beleata/fpga-led-panel-sram/hardware/pico-panel/preview/before-compact-connectors/placement-review.png

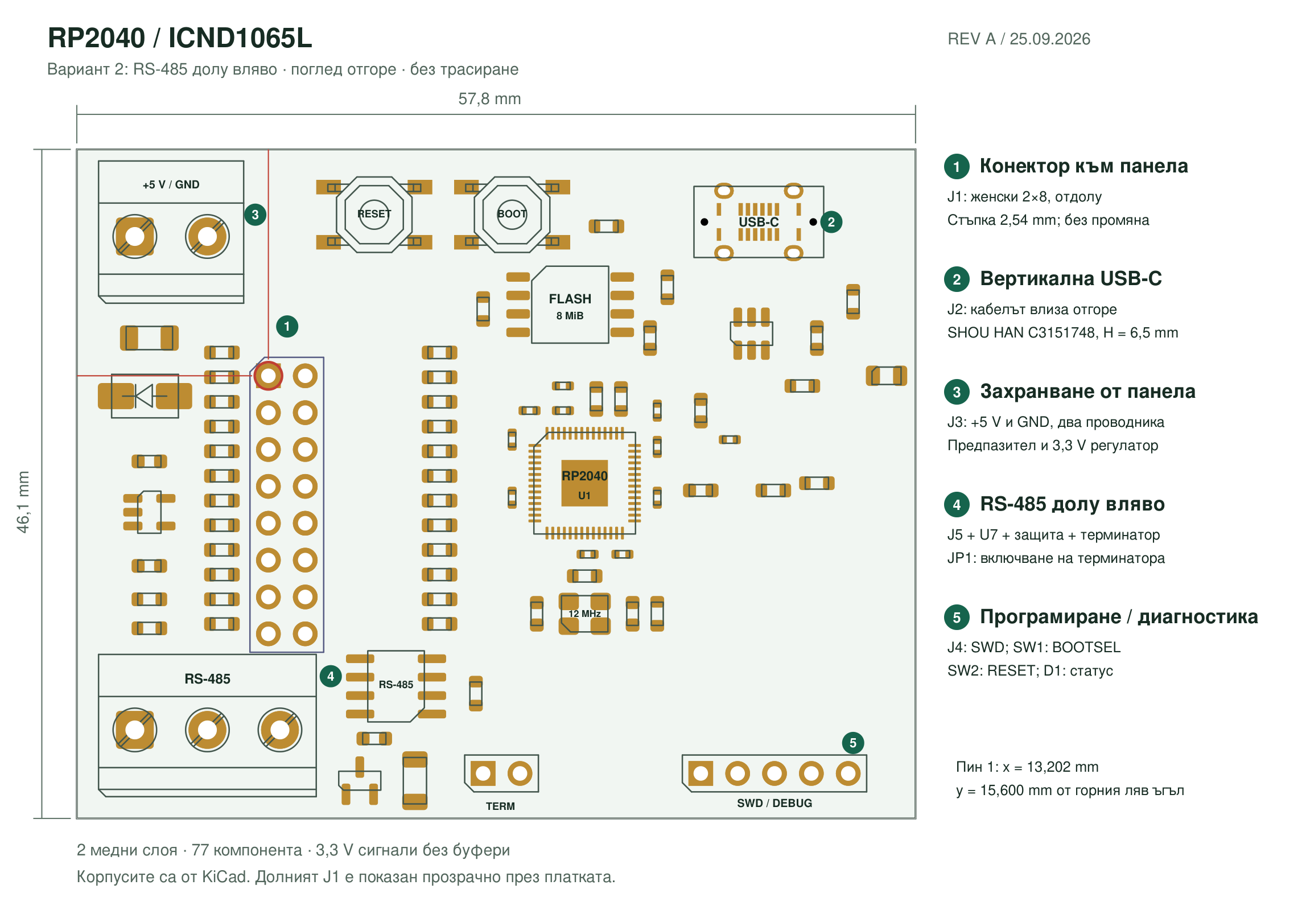
hardware/pico-panel/preview/before-compact-connectors/placement-review.png
