beleata/fpga-led-panel-sram/hardware/pico-panel/preview/placement-88mm.png

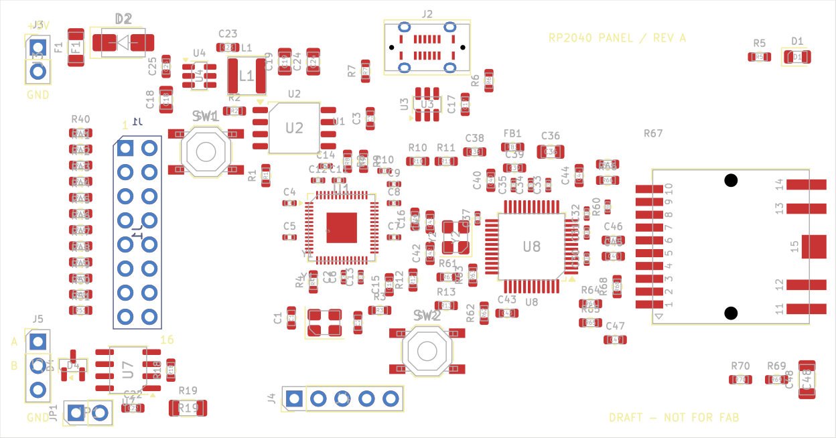
hardware/pico-panel/preview/placement-88mm.png
