beleata/fpga-led-panel-sram/hardware/pico-panel/preview/placement-before-rs485-move.png

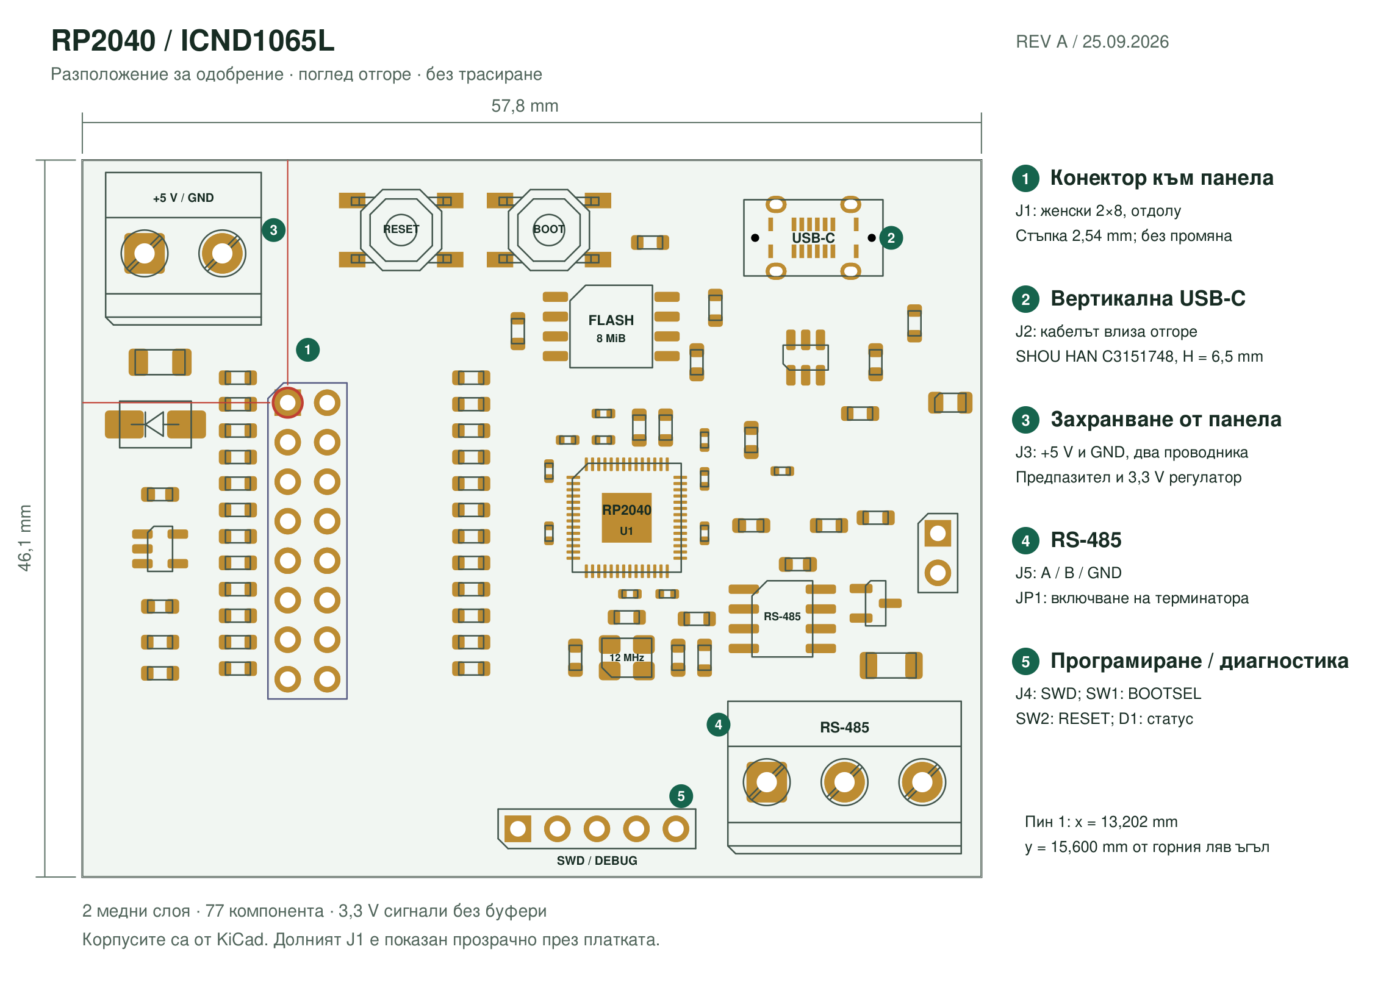
hardware/pico-panel/preview/placement-before-rs485-move.png
