beleata/fpga-led-panel-sram/hardware/pico-panel/preview/placement-review.png

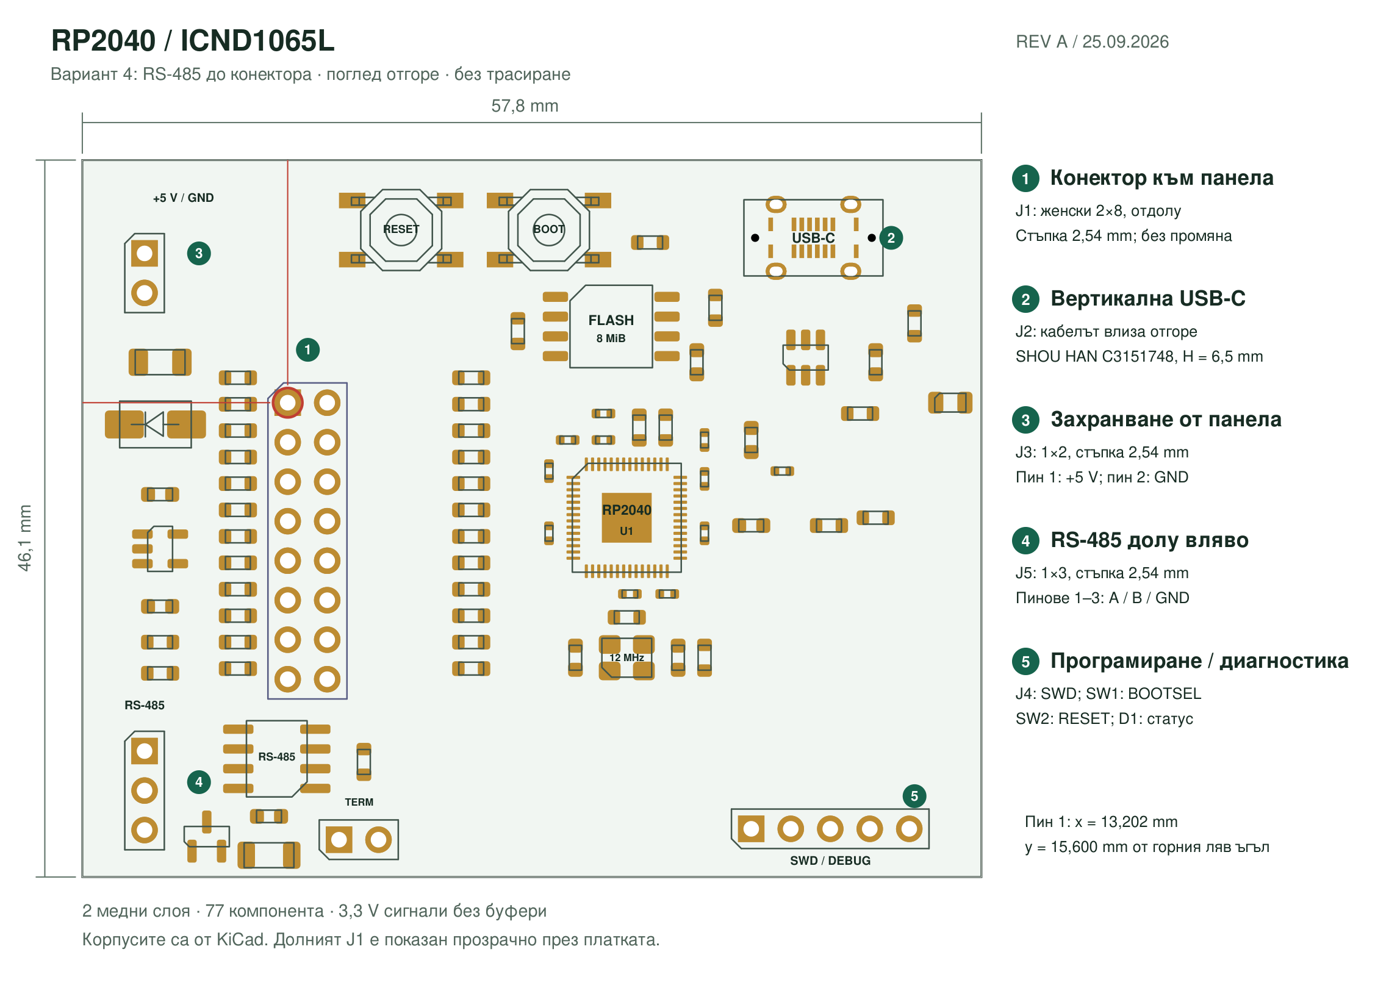
hardware/pico-panel/preview/placement-review.png
