beleata/fpga-led-panel-sram/hardware/pico-panel/preview/placement-top.png

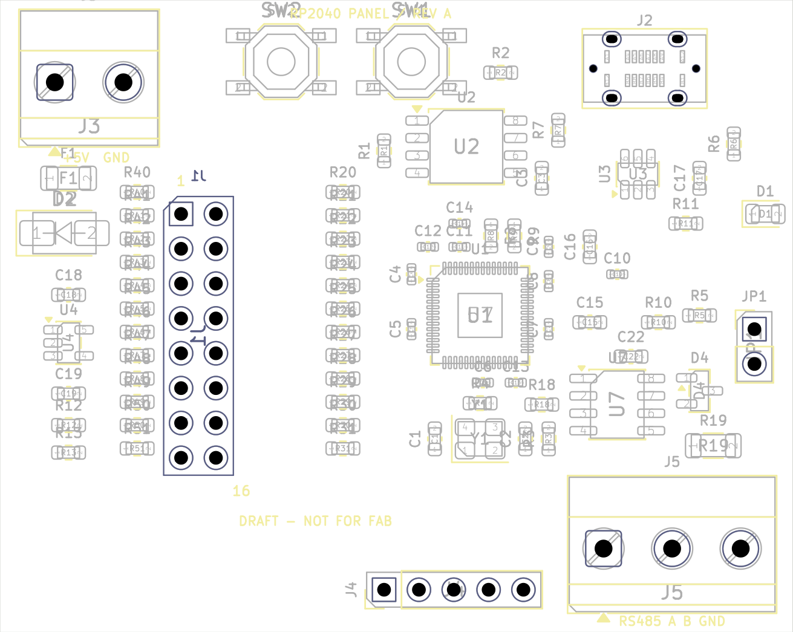
hardware/pico-panel/preview/placement-top.png
