beleata/fpga-led-panel-sram/hardware/pico-panel/preview/user-placement.png

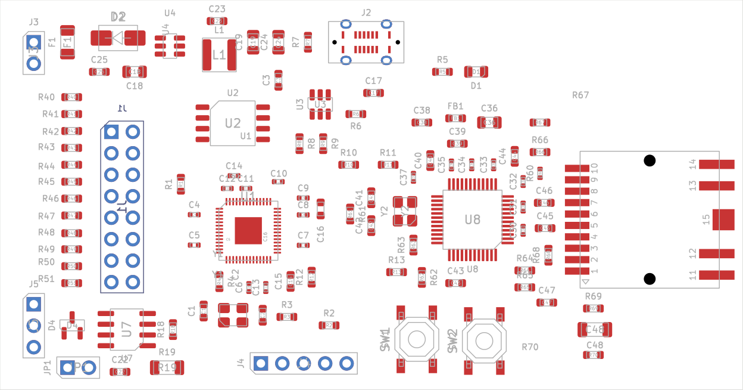
hardware/pico-panel/preview/user-placement.png
