beleata/fpga-led-panel-sram/hardware/pico-panel/reference/C3151748.png

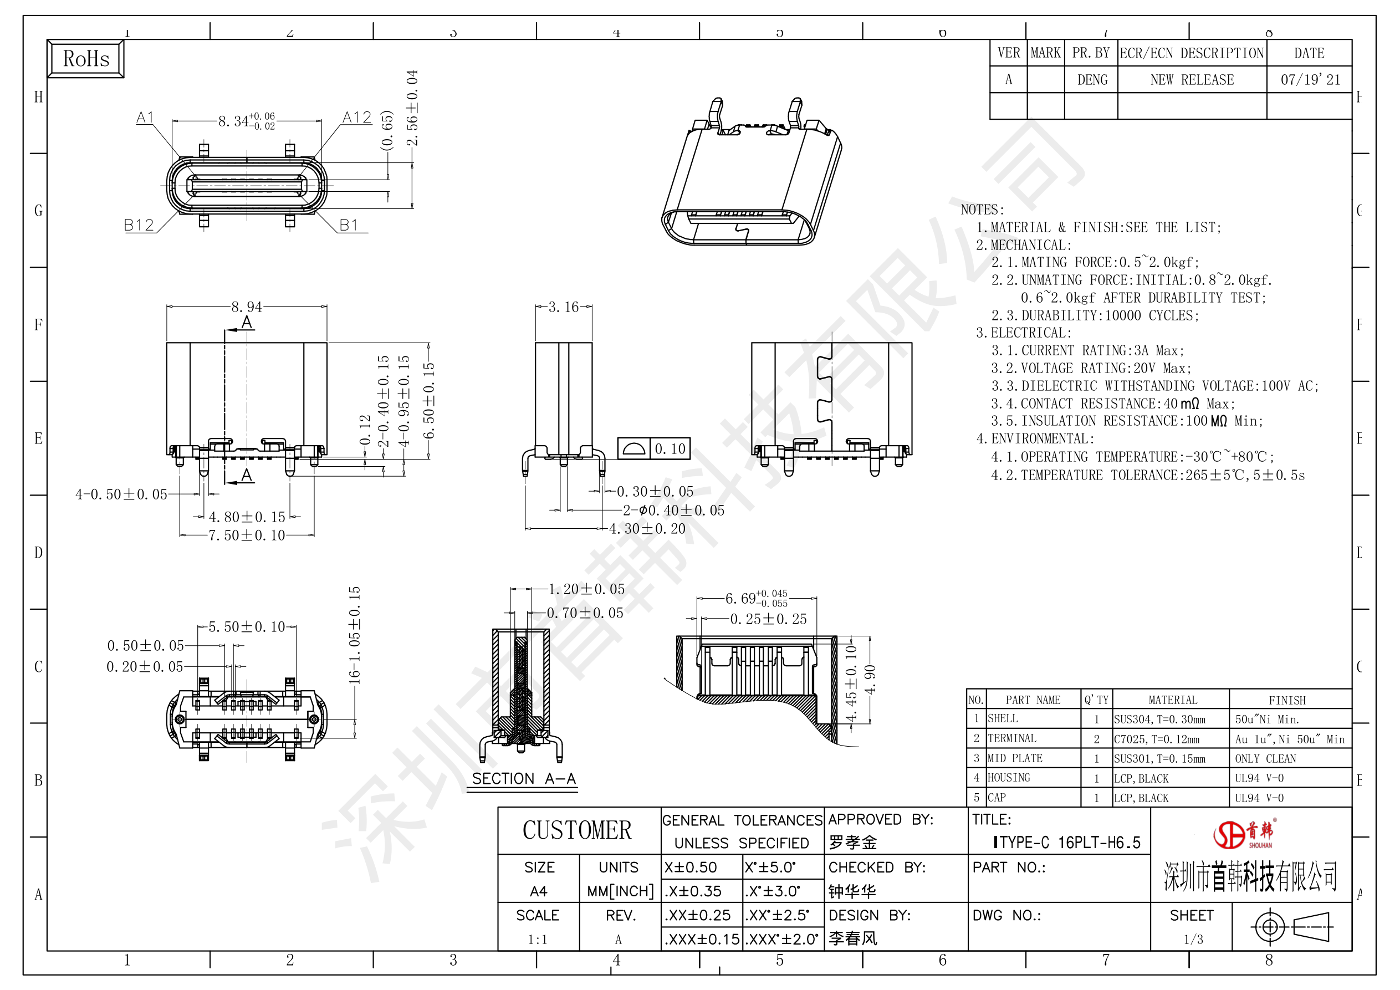
hardware/pico-panel/reference/C3151748.png
