beleata/fpga-led-panel-sram/hardware/pico-panel/reference/HR963380AE-footprint.png

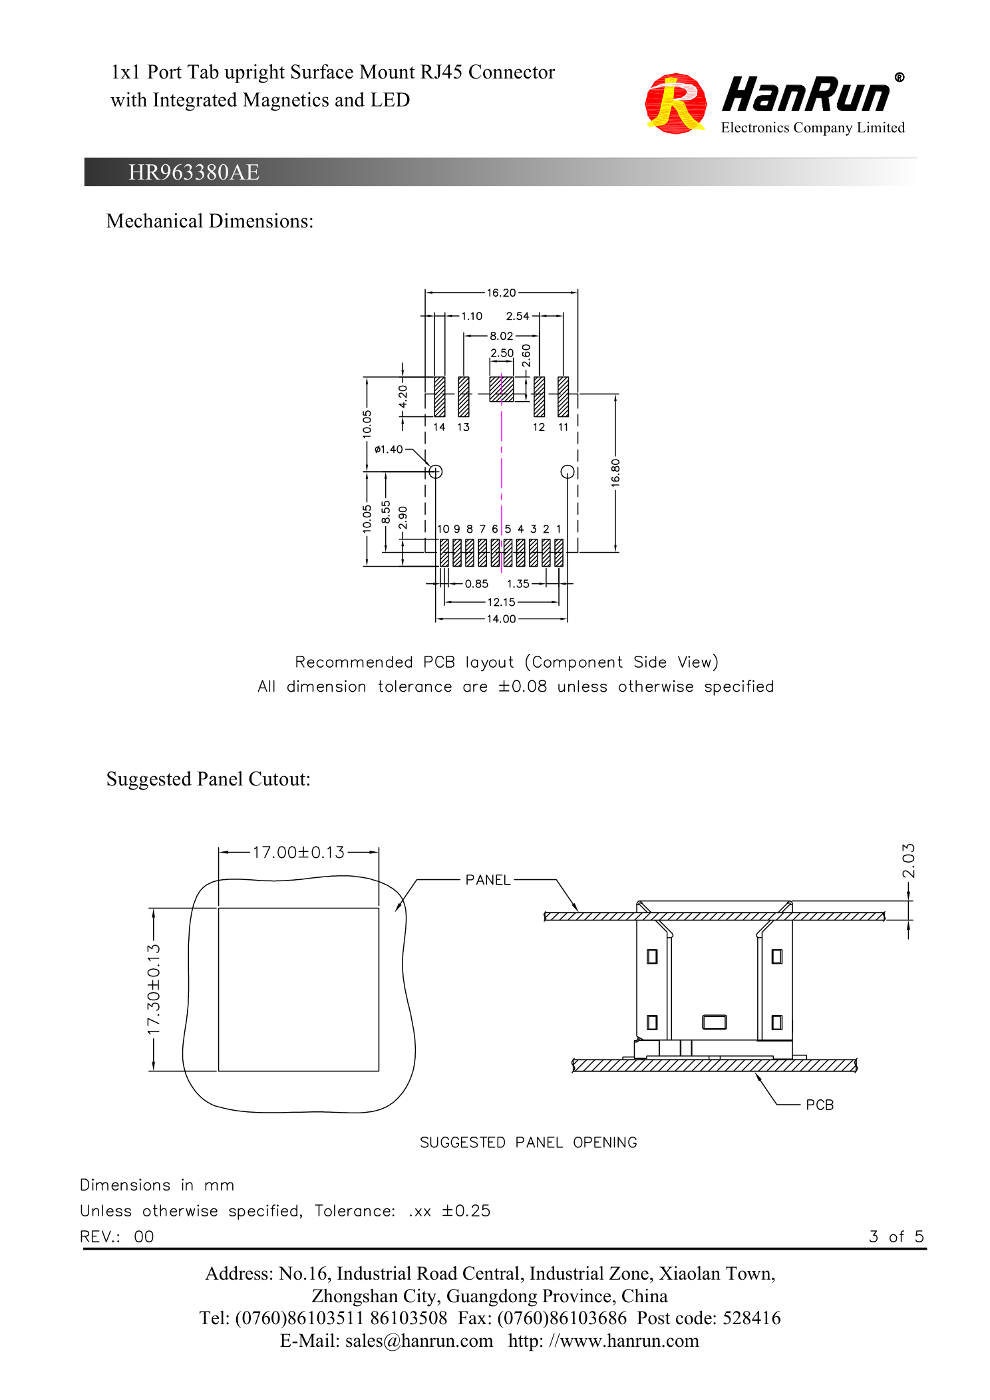
hardware/pico-panel/reference/HR963380AE-footprint.png
