beleata/fpga-led-panel-sram/hardware/pico-panel/reference/HR963380AE-land-detail.png

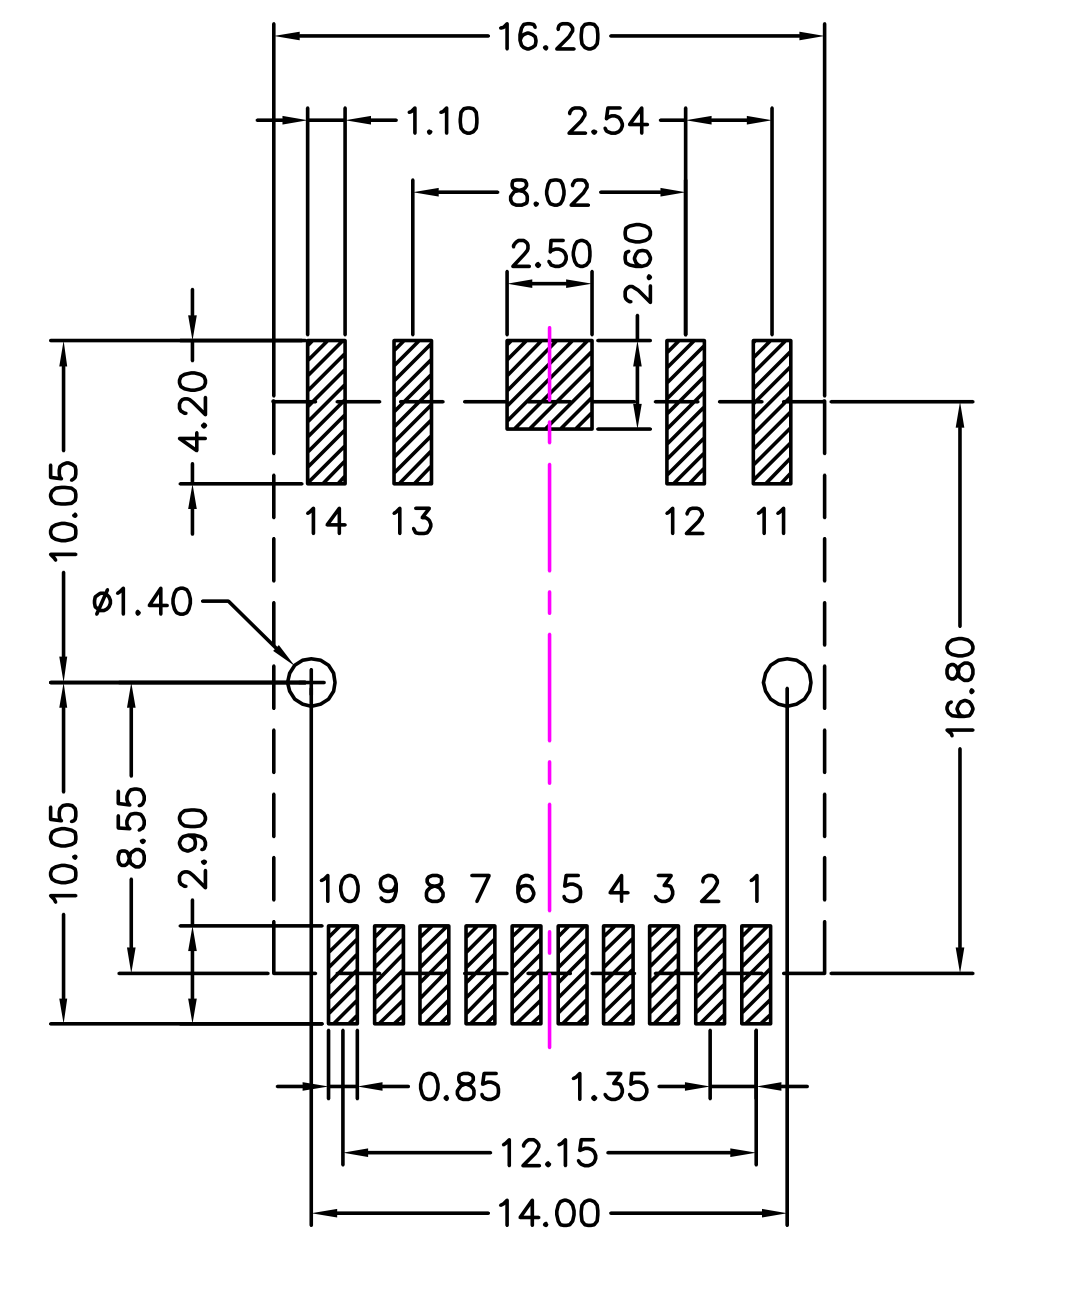
hardware/pico-panel/reference/HR963380AE-land-detail.png
