beleata/fpga-led-panel-sram/hardware/pico-panel/reference/HR963380AE.png

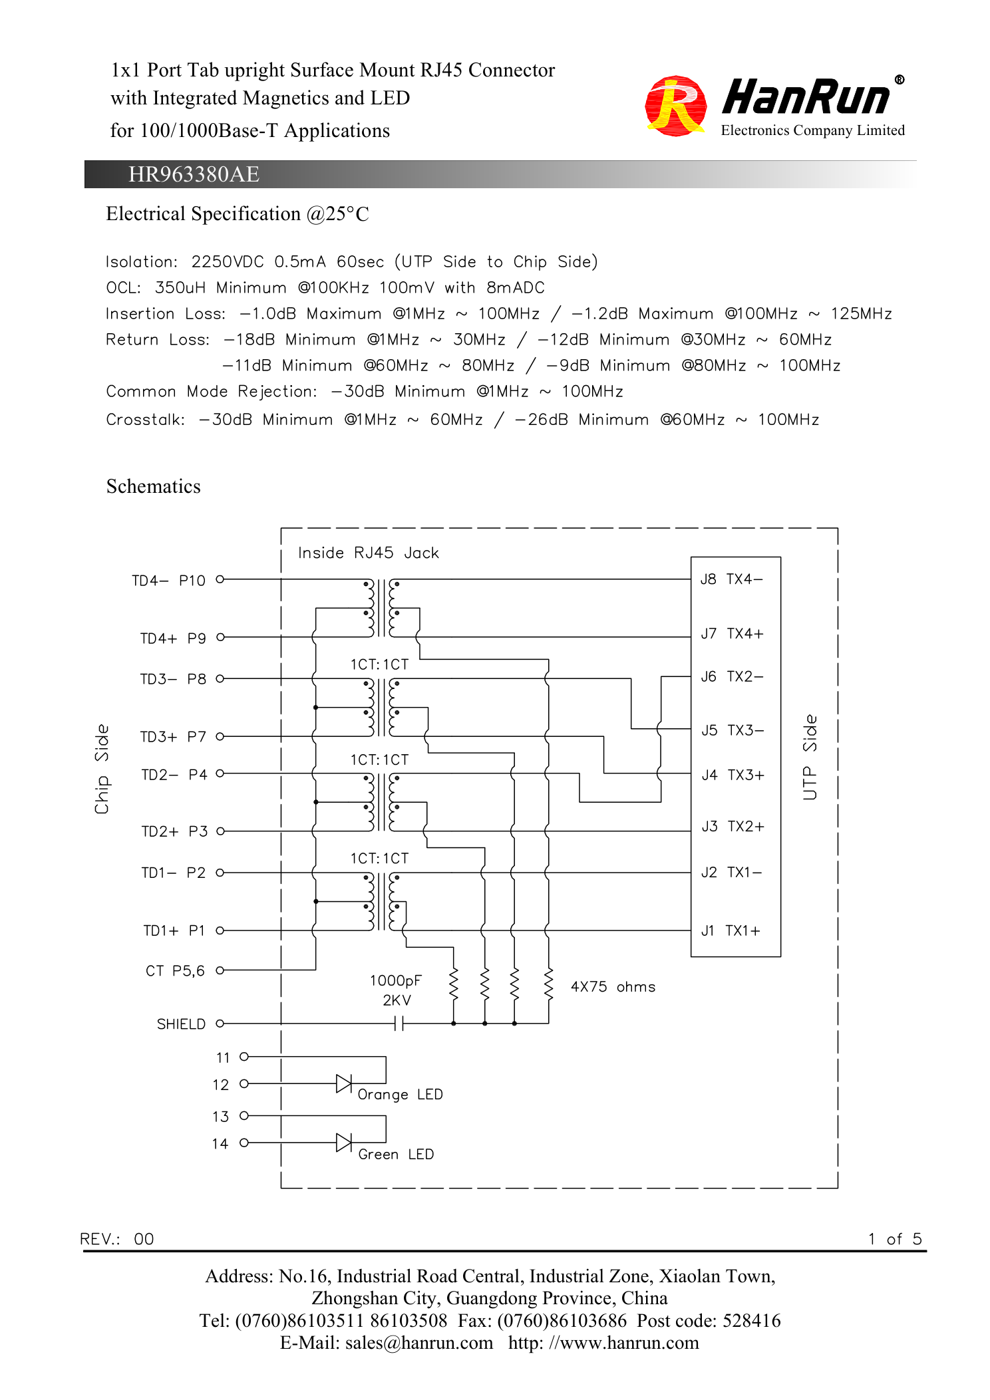
hardware/pico-panel/reference/HR963380AE.png
