beleata/fpga-led-panel-sram/hardware/pico-panel/reference/usb-landpattern-detail.png

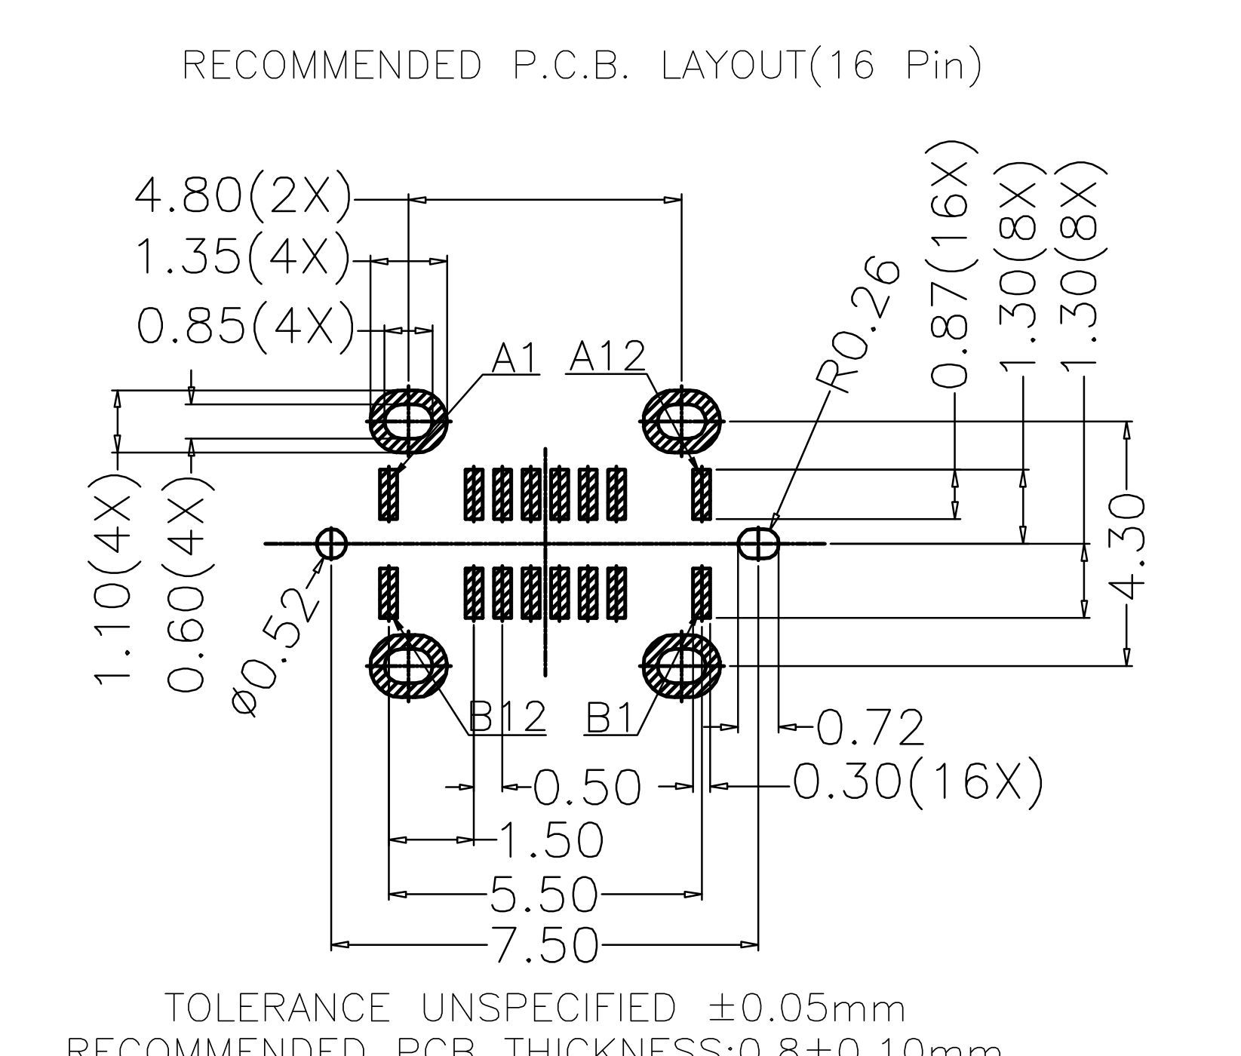
hardware/pico-panel/reference/usb-landpattern-detail.png
