beleata/fpga-led-panel-sram/panel/pattern-expected.png

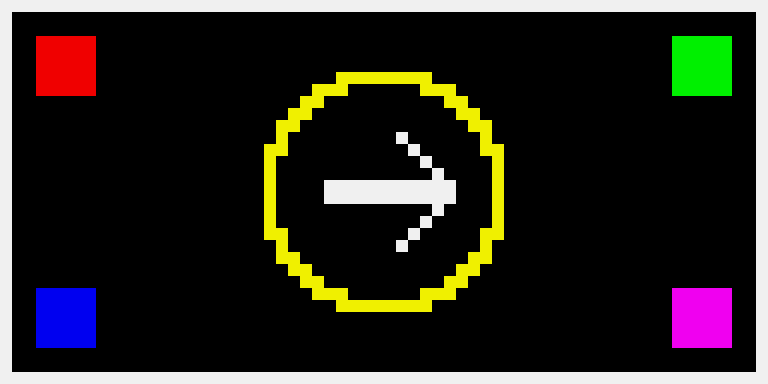
panel/pattern-expected.png
