beleata/fpga-led-panel-sram/video/animation-preview.png

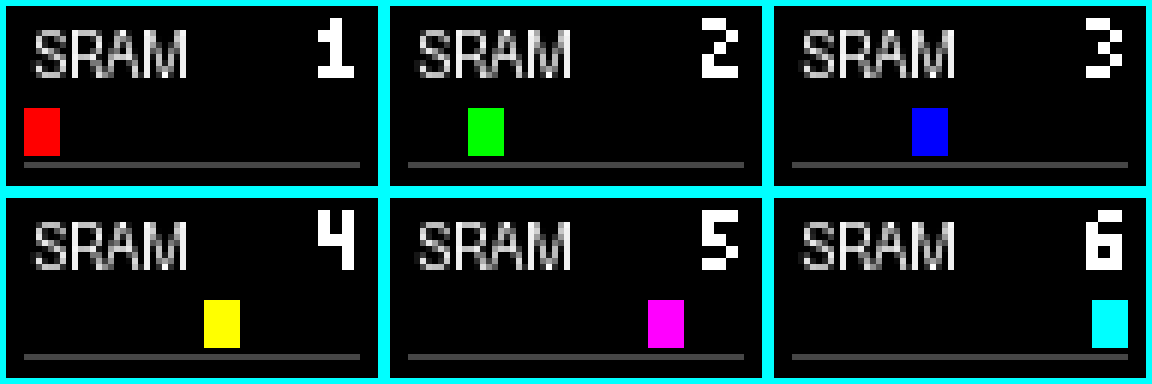
video/animation-preview.png
