beleata/fpga-led-panel-sram/video/last-sent-preview.png

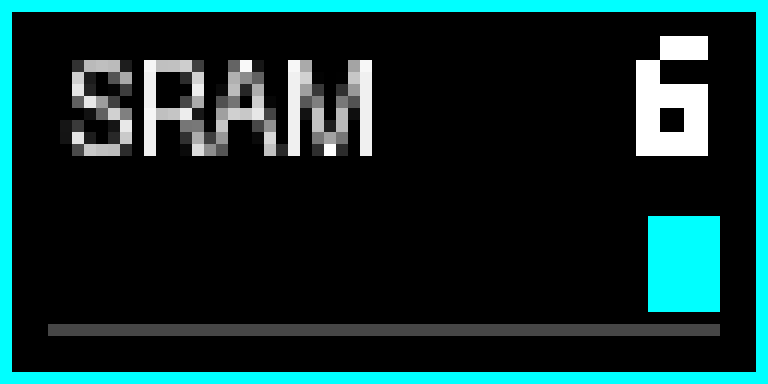
video/last-sent-preview.png
